Dakkaron/PEPit/SDCardContent/games/farm/gfx/background.bmp

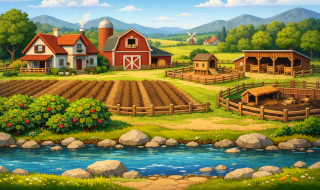
SDCardContent/games/farm/gfx/background.bmp
