Dakkaron/PEPit/SDCardContent/games/farm/gfx/farm1.bmp

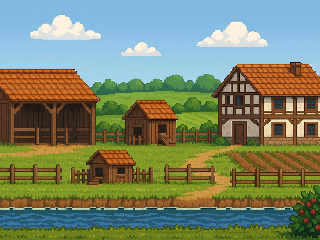
SDCardContent/games/farm/gfx/farm1.bmp
