Dakkaron/PEPit/SDCardContent/games/farm/gfx/farm1_c.bmp

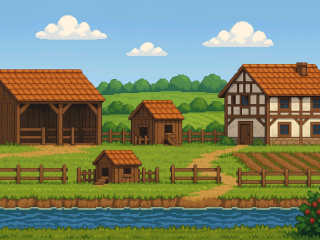
SDCardContent/games/farm/gfx/farm1_c.bmp
