Dakkaron/PEPit/SDCardContent/games/farm/gfx/farm2_c.bmp

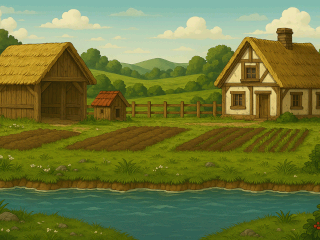
SDCardContent/games/farm/gfx/farm2_c.bmp
