Dakkaron/PEPit/SDCardContent/games/farm/gfx/farm3.bmp

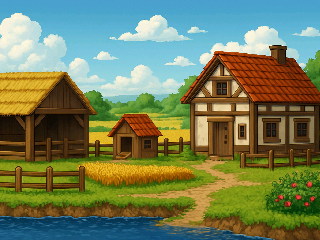
SDCardContent/games/farm/gfx/farm3.bmp
