Dakkaron/PEPit/SDCardContent/games/farm/gfx/farm3_c.bmp

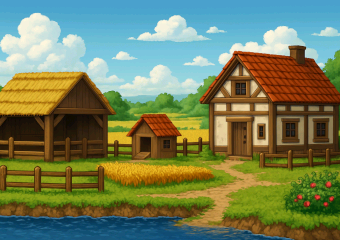
SDCardContent/games/farm/gfx/farm3_c.bmp
