Dakkaron/PEPit/SDCardContent/games/farm/gfx/field_tilled.bmp

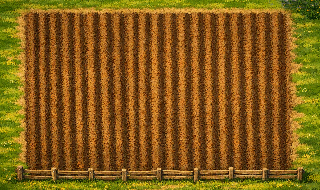
SDCardContent/games/farm/gfx/field_tilled.bmp
