Dakkaron/PEPit/SDCardContent/games/farm/gfx/fish.bmp

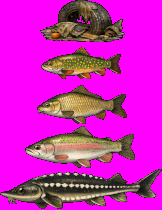
SDCardContent/games/farm/gfx/fish.bmp
