Dakkaron/PEPit/SDCardContent/games/farm/gfx/win/1.bmp

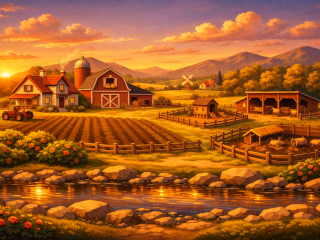
SDCardContent/games/farm/gfx/win/1.bmp
