Dakkaron/PEPit/SDCardContent/games/horserace/gfx/win/1.bmp

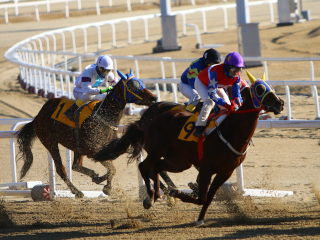
SDCardContent/games/horserace/gfx/win/1.bmp
