Dakkaron/PEPit/SDCardContent/games/plane/gfx/background.bmp

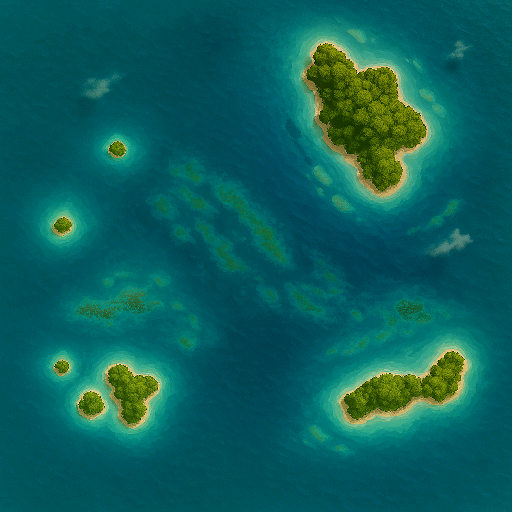
SDCardContent/games/plane/gfx/background.bmp
