Dakkaron/PEPit/SDCardContent/games/plane/gfx/win/win1.bmp

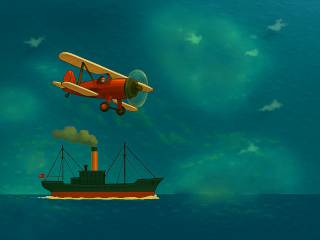
SDCardContent/games/plane/gfx/win/win1.bmp
