Dakkaron/PEPit/SDCardContent/gfx/manometerWinscreen.bmp

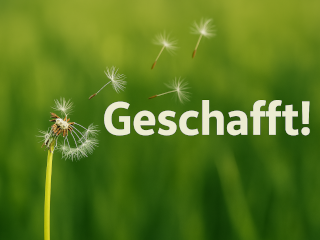
SDCardContent/gfx/manometerWinscreen.bmp
