Dakkaron/PEPit/SDCardContent/gfx/peps_1.5.bmp

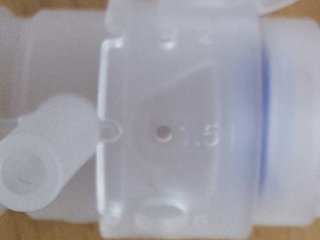
SDCardContent/gfx/peps_1.5.bmp
