Dakkaron/PEPit/SDCardContent/gfx/peps_2.bmp

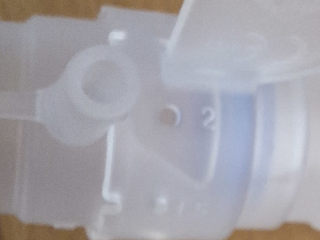
SDCardContent/gfx/peps_2.bmp
