Dakkaron/PEPit/SDCardContent/gfx/peps_3.bmp

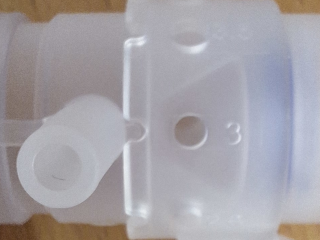
SDCardContent/gfx/peps_3.bmp
