Dakkaron/PEPit/SDCardContent/gfx/peps_4.5.bmp

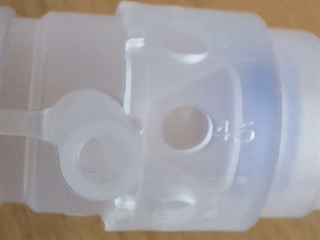
SDCardContent/gfx/peps_4.5.bmp
