Dakkaron/PEPit/SDCardContent/gfx/peps_4.bmp

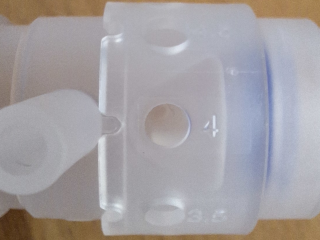
SDCardContent/gfx/peps_4.bmp
