Dakkaron/PEPit/T-HMI-PEPmonitor/src/hardware/pressuresensor.h

#ifndef __PRESSURESENSOR_H__
#define __PRESSURESENSOR_H__

#include <Arduino.h>
#include "constants.h"

void initPressureSensor(String* errorMessage);
void readPressure(BlowData* blowData);
void powerDownPressureSensor(bool down);

#endif /*PRESSURESENSOR*/
