Dakkaron/PEPit/T-HMI-PEPmonitor/src/physioProtocolHandler.cpp

#include "physioProtocolHandler.h"
#include "hardware/sdHandler.h"
#include "hardware/bluetoothHandler.h"
#include "hardware/wifiHandler.h"
#include "hardware/powerHandler.h"
#include "hardware/touchHandler.h"
#include "hardware/pressuresensor.h"
#include "hardware/serialHandler.h"
#include "games/games.h"
#include "constants.h"
#include "updateHandler.h"
#include "systemStateHandler.h"
#include "hardware/joystickHandler.h"

#define INHALE_ICON_PATH "/gfx/inhale.bmp"
#define EXHALE_ICON_PATH "/gfx/exhale.bmp"

static TFT_eSprite inhaleIcon(&tft);
static TFT_eSprite exhaleIcon(&tft);

ProfileData profileData{};
uint32_t currentTask;
uint32_t currentCycle;

BlowData blowData;
JumpData jumpData;

uint32_t lastMs = 0;

void runGameSelection(uint32_t requiredTaskTypes) {
  spr.fillSprite(TFT_BLACK);
  spr.pushSpriteFast(0,0);
  spr.fillSprite(TFT_BLACK);
  tft.fillScreen(TFT_BLACK);
  String errorMessage;
  uint16_t numberOfGames = getNumberOfGames(&errorMessage, requiredTaskTypes);
  checkFailWithMessage(errorMessage);
  Serial.print("Number of games: ");
  Serial.println(numberOfGames);
  String gamePath;
  if (numberOfGames == 0) {
    checkFailWithMessage("No fitting game found!");
  } else {
    gamePath = getGamePath(displayGameSelection(&spr, numberOfGames, requiredTaskTypes, &errorMessage), requiredTaskTypes, &errorMessage);
  }
  checkFailWithMessage(errorMessage);
  Serial.print("Game path: ");
  Serial.println(gamePath);
  displayFullscreenMessage("Spiel wird geladen\nBitte warten...");
  initGames(gamePath, &errorMessage);
  checkFailWithMessage(errorMessage);
}

uint32_t runProfileSelection() {
  String errorMessage;
  bool profileSuccessfullyLoaded = false;
  uint32_t requiredTaskTypes = 0;
  while (!profileSuccessfullyLoaded) {
    spr.fillSprite(TFT_BLACK);
    spr.pushSpriteFast(0,0);
    spr.fillSprite(TFT_BLACK);
    tft.fillScreen(TFT_BLACK);
    uint32_t totalNumberOfProfiles = getNumberOfProfiles(&errorMessage);
    checkFailWithMessage(errorMessage);
    int32_t selectedProfileId = displayProfileSelection(&spr, totalNumberOfProfiles, &errorMessage);
    profileSuccessfullyLoaded = true;
    if (selectedProfileId == PROGRESS_MENU_SELECTION_ID) {
      runGameSelection(REQUIRED_TASK_TYPE_PROGRESSION_MENU);
      uint32_t ms = millis();
      spr.fillSprite(TFT_BLACK);
      while (displayProgressionMenu(&spr, &errorMessage)) {
        checkFailWithMessage(errorMessage);
        lastMs = ms;
        ms = millis();
        doSystemTasks();
        spr.pushSpriteFast(0,0);
        spr.fillSprite(TFT_BLACK);
        handleSerial();
        vTaskDelay(1); // watchdog
      }
      tft.fillScreen(TFT_BLACK);
      deepSleepReset(); // Todo: don't restart, just go back to profile selection, but clear running game data
      
      profileSuccessfullyLoaded = false;
      continue;
    } else if (selectedProfileId == EXECUTION_LIST_SELECTION_ID) {
      spr.fillSprite(TFT_BLACK);
      spr.pushSpriteFast(0,0);
      tft.fillScreen(TFT_BLACK);
      char* executionLog;
      if (SD_MMC.exists(EXECUTION_LOG_PATH)) {
        executionLog = readFileToNewPSBuffer(EXECUTION_LOG_PATH);
      } else {
        executionLog = new char[1];
        executionLog[0] = '\0';
      }
      while (displayExecutionList(&spr, executionLog, &errorMessage)) {
        uint32_t ms = millis();
        checkFailWithMessage(errorMessage);
        lastMs = ms;
        ms = millis();
        doSystemTasks();
        spr.pushSpriteFast(0,0);
        spr.fillSprite(TFT_BLACK);
        handleSerial();
        vTaskDelay(1); // watchdog
      }
      delete(executionLog);
    } else if (selectedProfileId == SYSTEM_UPDATE_SELECTION_ID) {
      spr.fillSprite(TFT_BLACK);
      spr.pushSpriteFast(0,0);
      tft.fillScreen(TFT_BLACK);
      downloadAndRunSystemUpdate(&errorMessage);
      checkFailWithMessage(errorMessage);
      profileSuccessfullyLoaded = false; // Should never happen
      continue;
    }
    checkFailWithMessage(errorMessage);
    readProfileData(selectedProfileId, &profileData, &errorMessage);
    for (uint32_t i=0;i<profileData.tasks;i++) {
      if (profileData.taskType[i] == PROFILE_TASK_TYPE_SHORTBLOWS) {
        requiredTaskTypes |= REQUIRED_TASK_TYPE_SHORTBLOWS;
      } else if (profileData.taskType[i] == PROFILE_TASK_TYPE_LONGBLOWS) {
        requiredTaskTypes |= REQUIRED_TASK_TYPE_LONGBLOWS;
      } else if (profileData.taskType[i] == PROFILE_TASK_TYPE_EQUALBLOWS) {
        requiredTaskTypes |= REQUIRED_TASK_TYPE_EQUALBLOWS;
      } else if (profileData.taskType[i] == PROFILE_TASK_TYPE_INHALATION) {
        requiredTaskTypes |= REQUIRED_TASK_TYPE_INHALATION;
      } else if (profileData.taskType[i] == PROFILE_TASK_TYPE_INHALATIONPEP) {
        requiredTaskTypes |= REQUIRED_TASK_TYPE_INHALATIONPEP;
      } else if (profileData.taskType[i] == PROFILE_TASK_TYPE_TRAMPOLINE) {
        requiredTaskTypes |= REQUIRED_TASK_TYPE_TRAMPOLINE;
        spr.fillSprite(TFT_BLACK);
        spr.pushSpriteFast(0,0);
        spr.fillSprite(TFT_BLACK);
        tft.fillScreen(TFT_BLACK);
        if (!connectToTrampoline(false)) {
          displayFullscreenMessage("Verbinde mit Trampolin...\nTrampolinsensor einschalten!");
        }
        connectToTrampoline(true);
        break;
      }
    }
    vTaskDelay(1); // watchdog
  }
  for (uint32_t i=0;i<profileData.tasks;i++) {
    switch (profileData.taskType[i]) {
    case PROFILE_TASK_TYPE_LONGBLOWS:
      blowData.totalLongBlowRepetitions += profileData.taskRepetitions[i]*profileData.cycles;break;
    case PROFILE_TASK_TYPE_EQUALBLOWS:
      blowData.totalEqualBlowRepetitions += profileData.taskRepetitions[i]*profileData.cycles;break;
    case PROFILE_TASK_TYPE_SHORTBLOWS:
      blowData.totalShortBlowRepetitions += profileData.taskRepetitions[i]*profileData.cycles;break;
    }
  }
  blowData.totalCycleNumber = profileData.cycles;
  blowData.totalTaskNumber = profileData.tasks;
  jumpData.totalCycleNumber = profileData.cycles;
  jumpData.totalTaskNumber = profileData.tasks;
  while (touch.pressed()) {
    vTaskDelay(1);
  }
  return requiredTaskTypes;
}

inline static unsigned long getTaskDurationUntilLastAction() {
  return _max(1, (blowData.blowEndMs!=0 ? blowData.blowEndMs : blowData.taskStartMs) - blowData.taskStartMs);
}

inline static bool isTrampolineTask() {
  return profileData.taskType[currentTask] == PROFILE_TASK_TYPE_TRAMPOLINE;
}

inline static bool isInhalationPEPTask() {
  return profileData.taskType[currentTask] == PROFILE_TASK_TYPE_INHALATIONPEP;
}

inline static bool isInhalationPEPTaskActingLikePEP(BlowData* blowData) {
  return blowData->blowCount & 0x01;
}

inline static bool isInhalationTask() {
  return profileData.taskType[currentTask] == PROFILE_TASK_TYPE_INHALATION;
}

static void drawManometerModeDisplay() {
  spr.fillSprite(TFT_BLACK);
  if (isTrampolineTask()) {
    if (jumpData.msLeft > 0) {

      spr.setCursor(45, 100);
      spr.setTextSize(3);
      spr.print("Übrige Zeit: ");
      int32_t secondsLeft = _max(0, jumpData.msLeft/1000);
      spr.print(secondsLeft / 60);
      spr.print(":");
      if ((secondsLeft % 60) < 10) {
        spr.print("0");
      }
      spr.print(secondsLeft % 60);
    }
  } else {
    spr.drawCircle(SCREEN_WIDTH/2, SCREEN_HEIGHT/2, 100, 0xffff);
    spr.setTextDatum(CC_DATUM);
    spr.setTextSize(2);
    for (int32_t i=-30; i<=30; i+=1) {
      float angleInRadians = i*0.025*PI - PI*0.5;
      float cosI = cos(angleInRadians);
      float sinI = sin(angleInRadians);
      if (i % 10 == 0) {
        spr.drawString(String(i), SCREEN_WIDTH/2 + cosI*60, SCREEN_HEIGHT/2 + sinI*60);
        spr.drawLine(SCREEN_WIDTH/2 + cosI*100, SCREEN_HEIGHT/2 + sinI*100, SCREEN_WIDTH/2 + cosI*80, SCREEN_HEIGHT/2 + sinI*80, 0xffff);
      } else if (i % 5 == 0) {
        spr.drawLine(SCREEN_WIDTH/2 + cosI*100, SCREEN_HEIGHT/2 + sinI*100, SCREEN_WIDTH/2 + cosI*80, SCREEN_HEIGHT/2 + sinI*80, 0xffff);
      } else {
        spr.drawLine(SCREEN_WIDTH/2 + cosI*100, SCREEN_HEIGHT/2 + sinI*100, SCREEN_WIDTH/2 + cosI*90, SCREEN_HEIGHT/2 + sinI*90, 0xffff);
      }
    }
    spr.setTextSize(1);
    spr.setTextDatum(TL_DATUM);
    float angleInRadians = (float)(blowData.pressure)*0.025*PI - PI*0.5;
    float cosI = cos(angleInRadians);
    float sinI = sin(angleInRadians);
    if (cosI>-0.01 && cosI<0.01) {
      cosI = 0.0;
    }
    spr.drawLine(SCREEN_WIDTH*0.5, SCREEN_HEIGHT*0.5, SCREEN_WIDTH*0.5 + cosI*60.0, SCREEN_HEIGHT*0.5 + sinI*60.0, 0xffff);

    spr.fillRect(240, 210, 80, 30, TFT_BLUE);
    spr.setTextSize(2);
    if (blowData.cycleNumber >= blowData.totalCycleNumber-1 && blowData.taskNumber >= blowData.totalTaskNumber-1) {
      spr.drawString("Fertig", 255, 220);
    } else {
      spr.drawString("Weiter", 255, 220);
    }
  }
  doSystemTasks();
  spr.pushSpriteFast(0, 0);
}

static void drawInhalationDisplay() {
  spr.fillSprite(TFT_BLACK);
  String errorMessage;
  drawInhalationGame(&spr, &blowData, &errorMessage);
  drawProgressBar(&spr, blowData.currentlyBlowing ? (100 * (blowData.ms - blowData.blowStartMs) / blowData.targetDurationMs) : 0, 0, PRESSURE_BAR_X, PRESSURE_BAR_Y+25, PRESSURE_BAR_WIDTH, PRESSURE_BAR_HEIGHT);
  checkFailWithMessage(errorMessage);
  
  drawProgressBar(&spr, blowData.pressure, 10, PRESSURE_BAR_X, PRESSURE_BAR_Y, PRESSURE_BAR_WIDTH, PRESSURE_BAR_HEIGHT);
  spr.setTextSize(2);
  spr.setCursor(PRESSURE_BAR_X + 40, PRESSURE_BAR_Y - 14);
  printShaded(&spr, String(blowData.blowCount));
  
  spr.setCursor(PRESSURE_BAR_X + 80, PRESSURE_BAR_Y - 14);
  if (blowData.totalTaskNumber>1 && blowData.totalCycleNumber>1) {
    printShaded(&spr, String(blowData.taskNumber) + "/" + String(blowData.cycleNumber));
  } else if (blowData.totalTaskNumber>1) {
    printShaded(&spr, String(blowData.taskNumber));
  } else if (blowData.totalCycleNumber>1) {
    printShaded(&spr, String(blowData.cycleNumber));
  }
  
  if (blowData.blowCount >= blowData.totalBlowCount) {
    spr.fillRect(240, 210, 80, 30, TFT_BLUE);
    spr.drawString("Fertig", 255, 220);
  }

  doSystemTasks();
  spr.pushSpriteFast(0, 0);
}

static void drawInhaleExhaleIcons(BlowData* blowData) {
  if (!inhaleIcon.created()) {
    loadBmp(&inhaleIcon, INHALE_ICON_PATH);
    loadBmp(&exhaleIcon, EXHALE_ICON_PATH);
  }
  if (blowData->negativePressure) {
    inhaleIcon.pushToSprite(&spr, PRESSURE_BAR_X + PRESSURE_BAR_WIDTH - 32, PRESSURE_BAR_Y - 32, 0xf81f);
  } else {
    exhaleIcon.pushToSprite(&spr, PRESSURE_BAR_X + PRESSURE_BAR_WIDTH - 32, PRESSURE_BAR_Y - 32, 0xf81f);
  }
}

static void drawPEPDisplay() {
  spr.fillSprite(TFT_BLACK);
  String errorMessage;
  switch (blowData.taskType) {
    case PROFILE_TASK_TYPE_LONGBLOWS:
      drawLongBlowGame(&spr, &blowData, &errorMessage);break;
    case PROFILE_TASK_TYPE_EQUALBLOWS:
      drawEqualBlowGame(&spr, &blowData, &errorMessage);break;
    case PROFILE_TASK_TYPE_SHORTBLOWS:
      drawShortBlowGame(&spr, &blowData, &errorMessage);break;
    case PROFILE_TASK_TYPE_INHALATIONPEP:
      drawInhalationBlowGame(&spr, &blowData, &errorMessage);break;
  }
  drawProgressBar(&spr, blowData.currentlyBlowing ? (100 * (blowData.ms - blowData.blowStartMs) / blowData.targetDurationMs) : 0, 0, PRESSURE_BAR_X, PRESSURE_BAR_Y+25, PRESSURE_BAR_WIDTH, PRESSURE_BAR_HEIGHT);
  checkFailWithMessage(errorMessage);
  
  drawProgressBar(&spr, blowData.pressure, 10, PRESSURE_BAR_X, PRESSURE_BAR_Y, PRESSURE_BAR_WIDTH, PRESSURE_BAR_HEIGHT);
  spr.setTextSize(2);
  spr.setCursor(PRESSURE_BAR_X + 40, PRESSURE_BAR_Y - 14);
  printShaded(&spr, String(blowData.blowCount));
  
  spr.setCursor(PRESSURE_BAR_X + 80, PRESSURE_BAR_Y - 14);
  if (blowData.totalTaskNumber>1 && blowData.totalCycleNumber>1) {
    printShaded(&spr, String(blowData.taskNumber) + "/" + String(blowData.cycleNumber));
  } else if (blowData.totalTaskNumber>1) {
    printShaded(&spr, String(blowData.taskNumber));
  } else if (blowData.totalCycleNumber>1) {
    printShaded(&spr, String(blowData.cycleNumber));
  }
  
  if (blowData.taskType == PROFILE_TASK_TYPE_INHALATIONPEP) {
    drawInhaleExhaleIcons(&blowData);
    if (blowData.blowCount >= blowData.totalBlowCount) {
      spr.fillRect(240, 210, 80, 30, TFT_BLUE);
      spr.drawString("Fertig", 255, 220);
    }
  }

  doSystemTasks();
  spr.pushSpriteFast(0, 0);
}

static void drawTrampolineDisplay() {
  spr.fillSprite(TFT_BLACK);
  String errorMessage;
  drawTrampolineGame(&spr, &jumpData, &errorMessage);
  checkFailWithMessage(errorMessage);
  if (jumpData.msLeft > 0) {
    drawProgressBar(&spr, (100L*(jumpData.totalTime-jumpData.msLeft))/jumpData.totalTime, 0, PRESSURE_BAR_X, PRESSURE_BAR_Y, PRESSURE_BAR_WIDTH, PRESSURE_BAR_HEIGHT);
    spr.setTextSize(2);
    spr.drawString(String(jumpData.jumpCount) + "/" + String(jumpData.highscore), PRESSURE_BAR_X + 20, PRESSURE_BAR_Y - 14);
    spr.setCursor(100, 5);
    spr.setTextSize(3);
    int32_t secondsLeft = _max(0, jumpData.msLeft/1000);
    spr.print(secondsLeft / 60);
    spr.print(":");
    if ((secondsLeft % 60) < 10) {
      spr.print("0");
    }
    spr.print(secondsLeft % 60);
  }
  doSystemTasks();
  spr.pushSpriteFast(0, 0);
}

static void handleLogExecutions() {
  uint32_t textDatumBak = tft.getTextDatum();

  spr.fillSprite(TFT_BLACK);
  spr.setTextSize(2);
  spr.setTextDatum(TL_DATUM);
  spr.drawString("Datum und Uhrzeit", 20, 100);
  spr.drawString("werden abgerufen.", 20, 120);
  spr.drawString("Bitte warten...", 20, 140);
  spr.pushSpriteFast(0,0);

  String errorMessage;
  String ntpDateString, ntpTimeString;
  getFormattedTime(&ntpDateString, &ntpTimeString, &errorMessage);
  checkSoftFailWithMessage(errorMessage);
  if (!errorMessage.isEmpty()) {
    displayDateTimeSelection();
    errorMessage = "";
    getFormattedTime(&ntpDateString, &ntpTimeString, &errorMessage);
    checkSoftFailWithMessage(errorMessage);
    if (!errorMessage.isEmpty()) { // Should never happen
      ntpDateString = "N/A";
      ntpTimeString = "N/A";
      errorMessage = "";
    }
  }
  Serial.println("NTP Time: " + ntpDateString + " " + ntpTimeString);

  spr.fillSprite(TFT_BLACK);
  spr.setTextDatum(TC_DATUM);
  spr.setTextSize(2);
  spr.drawString("Schreibe Log auf SD-Karte", 160, 120);
  spr.drawString("NICHT AUSSCHALTEN!", 160, 140);
  spr.setTextDatum(textDatumBak);
  spr.pushSpriteFast(0,0);

  logExecutionToSD(&profileData, ntpDateString, ntpTimeString, blowData.successes, blowData.fails, blowData.totalTimeSpentBreathing, &errorMessage);
  checkFailWithMessage(errorMessage);
}

static void drawFinished() {
  static uint32_t winscreenTimeout = 0;
  static String winScreenPath = "";
  if (winscreenTimeout == 0) { // Only runs on first execution
    Serial.print("##### Start drawFinished(): ");
    Serial.println(millis());
    String errorMessage;
    Serial.print("##### Start handleLogExecutions(): ");
    Serial.println(millis());
    if (systemConfig.logExecutions) {
      handleLogExecutions();
    }
    Serial.print("##### initializing win screen: ");
    Serial.println(millis());
    endGame(&errorMessage);
    checkFailWithMessage(errorMessage);
    winscreenTimeout = millis() + WIN_SCREEN_TIMEOUT;
    spr.frameBuffer(1); // Clearing both frame buffers to get rid of old content
    spr.fillSprite(TFT_GREEN);
    spr.frameBuffer(2);
    spr.fillSprite(TFT_GREEN);
    spr.frameBuffer(1);
    spr.fillSprite(TFT_BLACK);
    spr.frameBuffer(2);
    spr.fillSprite(TFT_BLACK);
    spr.pushSpriteFast(0,0);
    tft.fillScreen(TFT_BLACK);
    Serial.print("##### start displaying win screen: ");
    Serial.println(millis());
    while (displayWinScreen(&spr, &errorMessage) && millis() < winscreenTimeout) {
      checkFailWithMessage(errorMessage);
      spr.pushSpriteFast(0,0);
      spr.fillSprite(TFT_BLACK);
      handleSerial();
      doSystemTasks();
      vTaskDelay(1); // watchdog
      if (isTouchInZone(0, 0, SCREEN_WIDTH, SCREEN_HEIGHT)) {
        winscreenTimeout = millis() + WIN_SCREEN_TIMEOUT;
      }
    }
    Serial.print("##### Display winscreen done: ");
    Serial.println(millis());
    if (systemConfig.manometerMode) {
      winScreenPath = MANOMETER_WINSCREEN_PATH;
    } else {
      winScreenPath = getRandomWinScreenPathForCurrentGame(&errorMessage);
      Serial.println("Win screen path: "+winScreenPath);
      checkFailWithMessage(errorMessage);
    }
    spr.frameBuffer(1);
    spr.fillSprite(TFT_BLACK);
    spr.frameBuffer(2);
    spr.fillSprite(TFT_BLACK);
    tft.fillScreen(TFT_BLACK);
    drawBmp(winScreenPath, 0, 0);
    if (getSystemUpdateAvailableStatus() == FIRMWARE_UPDATE_AVAILABLE) {
      uint32_t beforeShowUpdateTimeout = millis() + SHOW_SYSTEM_UPDATE_ON_WINSCREEN_TIMEOUT;
      Serial.print("Starting update timeout: ");
      Serial.print(beforeShowUpdateTimeout);
      Serial.print(" . ");
      Serial.println(millis());
      while (millis() < beforeShowUpdateTimeout) {
        spr.fillRect(32,0,66,20,TFT_BLACK);
        doSystemTasks();
        spr.pushSpriteFast(0,0);
        vTaskDelay(1); // watchdog
      }
      Serial.println("Ending update timeout.");

      tft.fillRect(25, 25, 270, 190, 0x001F);
      tft.fillRect(30, 30, 260, 180, 0x94b2);
      drawBmp("/gfx/systemupdate.bmp", 144, 35, false);
      // TODO: Add joystick controls for the update/reboot buttons
      tft.setTextColor(0xFFFF);
      tft.setTextSize(2);
      tft.setTextDatum(1);
      tft.drawString("Update verfügbar", 160, 80);
      tft.fillRect(60, 110, 200, 45, COLOR_BUTTON_PRIMARY);
      tft.drawString("Update jetzt starten", 160, 125);
      tft.fillRect(60, 160, 200, 45, COLOR_BUTTON_PRIMARY);
      tft.drawString("Neustart", 160, 175);
      bool isUpdateStarted = false;
      winscreenTimeout = millis() + WIN_SCREEN_TIMEOUT;
      Serial.print("Starting winscreen timeout: ");
      Serial.print(winscreenTimeout);
      Serial.print(" . ");
      Serial.println(millis());
      while (millis() < winscreenTimeout && !isUpdateStarted) {
        isUpdateStarted = isTouchInZone(60, 110, 200, 45);
        if (isTouchInZone(60, 160, 200, 45)) {
          tft.fillScreen(TFT_BLACK);
          deepSleepReset();
        }
        Serial.print(winscreenTimeout);
        Serial.print(" . ");
        Serial.print(millis());
        Serial.print(" - ");
        Serial.println(isUpdateStarted);
        spr.fillRect(32,0,66,20,TFT_BLACK);
        doSystemTasks();
        spr.pushSpriteFast(0,0);
        vTaskDelay(1); // watchdog
      }
      Serial.print("Ending winscreen timeout: ");
      Serial.println(isUpdateStarted);
      if (isUpdateStarted) {
        Serial.println("Starting update.");
        String errorMessage;
        tft.fillScreen(TFT_BLACK);
        downloadAndRunSystemUpdate(&errorMessage);
        checkFailWithMessage(errorMessage);
      } else {
        Serial.println("Power off.");
        power_off();
      }
    } else {
      tft.setTextDatum(1);
      tft.setTextColor(COLOR_BUTTON_PRIMARY_TEXT);
      if (isJoystickPresent()) {
        tft.fillRect(55, 175, 210, 55, TFT_YELLOW);
        tft.fillRect(58, 178, 204, 49, COLOR_BUTTON_PRIMARY);
      } else {
        tft.fillRect(55, 175, 210, 55, COLOR_BUTTON_PRIMARY_FRAME);
        tft.fillRect(60, 180, 200, 45, COLOR_BUTTON_PRIMARY);
      }
      tft.drawString("Neustart", 160, 195);
    }
  } else if (millis() > winscreenTimeout) {
    power_off();
  }
  if (getSystemUpdateAvailableStatus() != FIRMWARE_UPDATE_AVAILABLE && (isTouchInZone(60, 160, 200, 45) || getJoystickButton())) {
    tft.fillScreen(TFT_BLACK);
    deepSleepReset();
  }
  spr.fillRect(32,0,66,20,TFT_BLACK);
  doSystemTasks();
  spr.pushSpriteFast(0,0);
}

void displayPhysioRotateScreen() {
  if (profileData.taskChangeImagePath[currentTask].isEmpty() && profileData.taskChangeMessage[currentTask].isEmpty()) {
    return;
  }
  spr.fillSprite(TFT_BLACK);
  spr.pushSpriteFast(0, 0);
  spr.fillSprite(TFT_BLACK);
  spr.setTextSize(4);
  drawBmp(profileData.taskChangeImagePath[currentTask], 0, 0);
  spr.setTextDatum(TL_DATUM);
  spr.drawString(profileData.taskChangeMessage[currentTask], 5, 5);
  spr.pushSpriteFast(0, 0);
  uint32_t displayOkButtonMs = millis() + 5000;
  boolean joystickLocked = getJoystickButton();

  while (!isTouchInZone(230, 170, 80, 60) && (joystickLocked || !getJoystickButton())) {
    if (joystickLocked && !getJoystickButton()) {
      joystickLocked = false;
    }
    if (displayOkButtonMs!=0 && millis() > displayOkButtonMs) {
      spr.fillSprite(TFT_BLACK);
      spr.pushSpriteFast(0, 0);
      spr.fillSprite(TFT_BLACK);
      spr.setTextSize(4);
      drawBmp(profileData.taskChangeImagePath[currentTask], 0, 0);
      spr.setTextDatum(TL_DATUM);
      spr.drawString(profileData.taskChangeMessage[currentTask], 5, 5);
      if (isJoystickPresent()) {
        spr.fillRect(230, 170, 80, 60, TFT_YELLOW);
        spr.fillRect(233, 173, 74, 54, 0x18db);
      } else {
        spr.fillRect(230, 170, 80, 60, 0x18db);
      }
      spr.drawString("OK", 245, 185);
      spr.pushSpriteFast(0, 0);
      displayOkButtonMs = 0;
    }
    handleSerial();
    doSystemTasks();
    vTaskDelay(1); // watchdog
  }
  
  tft.fillScreen(TFT_BLACK);
  spr.fillScreen(TFT_BLACK);
  spr.pushSpriteFast(0, 0);
  delay(200);
}

inline static unsigned long getLastBlowEvent() {
  return blowData.currentlyBlowing ? blowData.blowStartMs : blowData.blowEndMs;
}

inline static bool isPepTask() {
  switch (profileData.taskType[currentTask]) {
    case PROFILE_TASK_TYPE_LONGBLOWS:
    case PROFILE_TASK_TYPE_EQUALBLOWS:
    case PROFILE_TASK_TYPE_SHORTBLOWS:
      return true;
    default:
      return false;
    }
}

void handlePhysioTask() {
  static uint32_t taskFinishedTimeout = 0;
  static bool touchBlocked = false;
  lastMs = blowData.ms;
  blowData.ms = millis();
  jumpData.ms = blowData.ms;
  if (blowData.taskStartMs == 0) {
    blowData.taskStartMs = blowData.ms;
  }
  if (isTrampolineTask()) {
    if (jumpData.msLeft < -5000) {
      currentCycle++;
      drawFinished(); //Todo: Make jump task compatible with multi-task configs
      return;
    }

    jumpData.cycleNumber = currentCycle;
    jumpData.taskNumber = currentTask;
    jumpData.totalTime = profileData.taskTime[currentTask];

    getJumpData(&jumpData, &profileData, currentTask);
  } else {
    blowData.taskNumber = currentTask;
    blowData.cycleNumber = currentCycle;
    blowData.totalBlowCount = profileData.taskRepetitions[currentTask];
    blowData.taskType = profileData.taskType[currentTask];
    if (isPepTask() || isInhalationTask() || (isInhalationPEPTask() && !isInhalationPEPTaskActingLikePEP(&blowData))) {
      blowData.targetPressure = profileData.taskTargetStrength[currentTask];
      blowData.minPressure = 100*profileData.taskMinStrength[currentTask]/profileData.taskTargetStrength[currentTask];
      blowData.negativePressure = profileData.taskNegativeStrength[currentTask];
      blowData.targetDurationMs = profileData.taskTime[currentTask];
    } else { // InhalationPEP task acting in PEP mode
      blowData.targetPressure = profileData.taskTargetStrength2[currentTask];
      blowData.minPressure = 100*profileData.taskMinStrength2[currentTask]/profileData.taskTargetStrength2[currentTask];
      blowData.negativePressure = profileData.taskNegativeStrength2[currentTask];
      blowData.targetDurationMs = profileData.taskTime2[currentTask];
    }

    if (currentCycle >= blowData.totalCycleNumber) {
      drawFinished();
      return;
    }
    readPressure(&blowData);
    if (blowData.pressure>blowData.minPressure && !blowData.currentlyBlowing) {
      Serial.print(F("Blowing... "));
      blowData.currentlyBlowing = true;
      blowData.blowStartMs = blowData.ms;
      blowData.peakPressure = 0;
      blowData.cumulativeError = 0;
      blowData.lastBlowStatus |= NEW_BLOW;
    } else if (blowData.pressure<=blowData.minPressure && blowData.currentlyBlowing) {
      blowData.blowEndMs = blowData.ms;
      blowData.totalTimeSpentBreathing += blowData.blowEndMs-blowData.blowStartMs;
      blowData.breathingScore = 200 * blowData.totalTimeSpentBreathing / getTaskDurationUntilLastAction();
      Serial.print(blowData.blowEndMs-blowData.blowStartMs);
      Serial.println(F("ms"));
      blowData.currentlyBlowing = false;
      Serial.print(F("Ending blow"));
      if (blowData.ms-blowData.blowStartMs > blowData.targetDurationMs) {
        blowData.blowCount++;
        blowData.lastBlowStatus = LAST_BLOW_SUCCEEDED;
        blowData.successes++;
        Serial.println(F(" successfully"));
        Serial.print(F(" Blowstart:       "));
        Serial.println(blowData.blowStartMs);
        Serial.print(F(" Blowend:         "));  
        Serial.println(blowData.blowEndMs);
        Serial.print(F(" Target Duration: "));
        Serial.println(blowData.targetDurationMs);
        // Check for task end on PEP tasks
        if (!systemConfig.manometerMode && isPepTask() && taskFinishedTimeout==0 && blowData.blowCount >= blowData.totalBlowCount) {
          taskFinishedTimeout = blowData.ms + 2000;
        }
      } else {
        blowData.fails++;
        blowData.lastBlowStatus = LAST_BLOW_FAILED;
      }
    }
    // Check for task end on inhalation tasks
    if (blowData.blowCount >= blowData.totalBlowCount) {
      if (isTouchInZone(240, 210, 80, 30)) {
        taskFinishedTimeout = blowData.ms;
        tft.invertDisplay(0);
      } else if ((isInhalationTask() || isInhalationPEPTask()) && !blowData.currentlyBlowing && blowData.ms-getLastBlowEvent() > INHALATION_TASK_END_TIMEOUT && taskFinishedTimeout==0) {
        taskFinishedTimeout = blowData.ms;
        tft.invertDisplay(0);
      } else if ((isInhalationTask() || isInhalationPEPTask()) && !blowData.currentlyBlowing && blowData.ms-getLastBlowEvent() > INHALATION_TASK_WARN_TIMEOUT) {
        tft.invertDisplay((blowData.ms/500) % 2);
      } else {
        tft.invertDisplay(0);
      }
    }
    if (systemConfig.manometerMode && !touchBlocked && isTouchInZone(240, 210, 80, 30)) {
      if (isTouchInZone(240, 210, 80, 30)) {
        taskFinishedTimeout = blowData.ms;
        tft.invertDisplay(0);
      }
    }
    blowData.peakPressure = _max(blowData.peakPressure, blowData.pressure);
    if (taskFinishedTimeout!=0 && blowData.ms > taskFinishedTimeout) {
      Serial.println();
      Serial.println("##### DISPLAY ROTATE ######");
      Serial.print("    Rotating to: ");
      switch (blowData.taskType) {
        case PROFILE_TASK_TYPE_EQUALBLOWS:
          Serial.print("Equal blows");break;
        case PROFILE_TASK_TYPE_LONGBLOWS:
          Serial.print("Long blows");break;
        case PROFILE_TASK_TYPE_SHORTBLOWS:
          Serial.print("Short blows");break;
        case PROFILE_TASK_TYPE_TRAMPOLINE:
          Serial.print("Trampoline");break;
        case PROFILE_TASK_TYPE_INHALATION:
          Serial.print("Inhalation");break;
        case PROFILE_TASK_TYPE_INHALATIONPEP:
          Serial.print("Inhalation+PEP");break;
      }
      Serial.println();
      currentTask++;
      if (currentTask >= profileData.tasks) {
        currentCycle++;
        currentTask = 0;
      }
      blowData.blowCount = 0;
      blowData.lastBlowStatus = 0;
      blowData.taskStartMs = blowData.ms;
      taskFinishedTimeout = 0;
      if (currentCycle < blowData.totalCycleNumber) {
        displayPhysioRotateScreen();
      }
    }
  }

  if (systemConfig.manometerMode) {
    drawManometerModeDisplay();
  } else if (isPepTask() || isInhalationPEPTask()) {
    drawPEPDisplay();
  } else if (isInhalationTask()) {
    drawInhalationDisplay();
  } else if (isTrampolineTask()) {
    drawTrampolineDisplay();
  }
  if (!isTouchInZone(0, 0, SCREEN_WIDTH, SCREEN_HEIGHT)) {
    touchBlocked = false;
  }
}
