Dakkaron/PEPit/T-HMI-PEPmonitor/src/hardware/MyFont.h

/**
 * Created with gfx-fe (github.com/arnoson/gfx-fe): a web based editor for gfx fonts.
 * Editor Settings: {"canvas":{"width":8,"height":8},"metrics":{},"baseline":2,"basedOn":{"name":"","size":12,"guides":true,"threshold":125}}
 */

const uint8_t Font5x7FixedBitmaps[] PROGMEM = {
  0xfa, 0xb4, 0x52, 0xbe, 0xaf, 0xa9, 0x40, 0x23, 0xe8, 0xe2, 0xf8, 0x80,
  0xc6, 0x44, 0x44, 0x4c, 0x60, 0x64, 0xa8, 0x8a, 0xc9, 0xa0, 0xd8, 0x6a,
  0xa4, 0x95, 0x58, 0x25, 0x5d, 0xf7, 0x54, 0x80, 0x21, 0x3e, 0x42, 0x00,
  0xd0, 0xf8, 0xf0, 0x08, 0x88, 0x88, 0x00, 0x74, 0x67, 0x5c, 0xc5, 0xc0,
  0x59, 0x24, 0xb8, 0x74, 0x42, 0x22, 0x23, 0xe0, 0xf8, 0x88, 0x20, 0xc5,
  0xc0, 0x11, 0x95, 0x2f, 0x88, 0x40, 0xfc, 0x21, 0xe0, 0xc5, 0xc0, 0x32,
  0x21, 0xe8, 0xc5, 0xc0, 0xf8, 0x44, 0x44, 0x21, 0x00, 0x74, 0x62, 0xe8,
  0xc5, 0xc0, 0x74, 0x62, 0xf0, 0x89, 0x80, 0xf3, 0xc0, 0xf3, 0x60, 0x12,
  0x48, 0x42, 0x10, 0xf8, 0x3e, 0x84, 0x21, 0x24, 0x80, 0x74, 0x42, 0x22,
  0x00, 0x80, 0x74, 0x6b, 0x7b, 0xc1, 0xc0, 0x22, 0xa3, 0xf8, 0xc6, 0x20,
  0xf4, 0x63, 0xe8, 0xc7, 0xc0, 0x74, 0x61, 0x08, 0x45, 0xc0, 0xe4, 0xa3,
  0x18, 0xcb, 0x80, 0xfc, 0x21, 0xe8, 0x43, 0xe0, 0xfc, 0x21, 0xe8, 0x42,
  0x00, 0x74, 0x61, 0x38, 0xc5, 0xc0, 0x8c, 0x63, 0xf8, 0xc6, 0x20, 0xe9,
  0x24, 0xb8, 0x38, 0x84, 0x21, 0x49, 0x80, 0x8c, 0xa9, 0x8a, 0x4a, 0x20,
  0x84, 0x21, 0x08, 0x43, 0xe0, 0x8e, 0xeb, 0x18, 0xc6, 0x20, 0x8c, 0x73,
  0x59, 0xc6, 0x20, 0x74, 0x63, 0x18, 0xc5, 0xc0, 0xf4, 0x63, 0xe8, 0x42,
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
  {    0,    0,    0,    0,    0,    0 }, // 0xb7 '·'
  {    0,    0,    0,    0,    0,    0 }, // 0xb8 '¸'
  {    0,    0,    0,    0,    0,    0 }, // 0xb9 '¹'
  {    0,    0,    0,    0,    0,    0 }, // 0xba 'º'
  {    0,    0,    0,    0,    0,    0 }, // 0xbb '»'
  {    0,    0,    0,    0,    0,    0 }, // 0xbc '¼'
  {    0,    0,    0,    0,    0,    0 }, // 0xbd '½'
  {    0,    0,    0,    0,    0,    0 }, // 0xbe '¾'
  {    0,    0,    0,    0,    0,    0 }, // 0xbf '¿'
  {    0,    0,    0,    0,    0,    0 }, // 0xc0 'À'
  {    0,    0,    0,    0,    0,    0 }, // 0xc1 'Á'
  {    0,    0,    0,    0,    0,    0 }, // 0xc2 'Â'
  {    0,    0,    0,    0,    0,    0 }, // 0xc3 'Ã'
  {  356,    5,    7,    6,    0,    0 }, // 0xc4 'Ä'
  {    0,    0,    0,    0,    0,    0 }, // 0xc5 'Å'
  {    0,    0,    0,    0,    0,    0 }, // 0xc6 'Æ'
  {    0,    0,    0,    0,    0,    0 }, // 0xc7 'Ç'
  {    0,    0,    0,    0,    0,    0 }, // 0xc8 'È'
  {    0,    0,    0,    0,    0,    0 }, // 0xc9 'É'
  {    0,    0,    0,    0,    0,    0 }, // 0xca 'Ê'
  {    0,    0,    0,    0,    0,    0 }, // 0xcb 'Ë'
  {    0,    0,    0,    0,    0,    0 }, // 0xcc 'Ì'
  {    0,    0,    0,    0,    0,    0 }, // 0xcd 'Í'
  {    0,    0,    0,    0,    0,    0 }, // 0xce 'Î'
  {    0,    0,    0,    0,    0,    0 }, // 0xcf 'Ï'
  {    0,    0,    0,    0,    0,    0 }, // 0xd0 'Ð'
  {    0,    0,    0,    0,    0,    0 }, // 0xd1 'Ñ'
  {    0,    0,    0,    0,    0,    0 }, // 0xd2 'Ò'
  {    0,    0,    0,    0,    0,    0 }, // 0xd3 'Ó'
  {    0,    0,    0,    0,    0,    0 }, // 0xd4 'Ô'
  {    0,    0,    0,    0,    0,    0 }, // 0xd5 'Õ'
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
};

const GFXfont Font5x7Fixed PROGMEM = {
  (uint8_t *)Font5x7FixedBitmaps,
  (GFXglyph *)Font5x7FixedGlyphs,
  32, 252, 8
};
