Dakkaron/PEPit/T-HMI-PEPmonitor/src/hardware/wifiHandler.cpp

#include "wifiHandler.h"
#include <WiFi.h>
#include <ArduinoJson.h>
#include <HTTPClient.h>
#include "sdHandler.h"
#include "esp32-hal.h"

static uint8_t wifiStatus = WIFI_CONNECTION_SEARCHING;

uint8_t getWifiStatus() {
  return wifiStatus;
}

uint8_t startWifi() {
  String ssid = "";
  String password = "";
  if (wifiStatus == WIFI_CONNECTION_OK) {
    return wifiStatus;
  }
  int32_t networksFound = WiFi.scanNetworks();
  for (int32_t wifiNumber=0; wifiNumber<MAX_WIFI_NETWORKS; wifiNumber++) {
    Serial.println("Starting WIFI");
    WiFi.mode(WIFI_STA);
    switch (wifiNumber) {
      case 0:
        ssid = systemConfig.wifiSsid;
        password = systemConfig.wifiPassword;
        break;
      case 1:
        ssid = systemConfig.wifiSsid2;
        password = systemConfig.wifiPassword2;
        break;
      case 2:
        ssid = systemConfig.wifiSsid3;
        password = systemConfig.wifiPassword3;
        break;
    }
    Serial.print(wifiNumber+1);
    Serial.print("/");
    Serial.println(MAX_WIFI_NETWORKS);
    Serial.println(ssid);
    Serial.println(password);
    bool wifiFound = false;
    for (int32_t i=0;i<networksFound;i++) {
      if (WiFi.SSID(i) == ssid) {
        wifiFound = true;
        break;
      }
    }
    if (!wifiFound) {
      Serial.println("Wifi not found");
      wifiStatus = WIFI_CONNECTION_NOWIFI;
      continue;
    }
    WiFi.begin(ssid, password);
    Serial.print("Connecting to WIFI");
    for (uint8_t i=0;i<WIFI_RETRY_COUNT;i++) {
      if (WiFi.status() != WL_CONNECTED) {
        Serial.print('.');
        delay(1000);
      } else {
        wifiStatus = WIFI_CONNECTION_OK;
        Serial.println("done");
        return wifiStatus;
      }
    }
    Serial.println("Failed to connect to WIFI "+ssid);
  }
  Serial.println("ENDING WIFI CONNECT");
  return wifiStatus;
}

static String leftPad(String s, uint16_t len, String c) {
  uint32_t charsToAdd = len-s.length();
  for (uint32_t i=0; i<charsToAdd; i++) {
    s = c + s;
  }
  return s;
}

void getFormattedTime(String* ntpDateString, String* ntpTimeString, String* errorMessage) {
  static int32_t lastWifiStatus = -1;
  static bool getLocalTimeFailedBefore = false;
  struct tm timeinfo;
  if((wifiStatus==lastWifiStatus && getLocalTimeFailedBefore) || !getLocalTime(&timeinfo,1)){
    if (!(wifiStatus==lastWifiStatus && getLocalTimeFailedBefore)) {
      Serial.println("Failed to obtain time from NTP");
    }
    getLocalTimeFailedBefore = true;
    lastWifiStatus = wifiStatus;
    errorMessage->concat("Konnte Zeit nicht abrufen.\n");
    errorMessage->concat("Wahrscheinlich WLAN-Verbindungsproblem.\n");
    *ntpDateString = "N/A";
    *ntpTimeString = "N/A";
    return;
  }
  *ntpDateString = String(timeinfo.tm_year+1900) + "-" + String(timeinfo.tm_mon+1) + "-" + String(timeinfo.tm_mday);
  *ntpTimeString = leftPad(String(timeinfo.tm_hour), 2, "0") + ":" + leftPad(String(timeinfo.tm_min), 2, "0");
}

void downloadFile(String url, String filename, String* errorMessage, THandlerFunction_Progress progressCallback) {
  // Get file stream from internet
  uint32_t connectionStatus = startWifi();
  if (connectionStatus == WIFI_CONNECTION_NOWIFI) {
    errorMessage->concat("Failed to download file from ");
    errorMessage->concat(url);
    errorMessage->concat(" because of missing WIFI connection");
    return;
  }

  HTTPClient httpClient;
  httpClient.setFollowRedirects(HTTPC_STRICT_FOLLOW_REDIRECTS);
  Serial.println("downloadFile("+url+", "+filename+")");
  httpClient.begin(url);
  int httpCode = httpClient.GET();
  if (httpCode != 200) {
    errorMessage->concat("HTTP error: "+String(httpCode));
    return;
  }
  WiFiClient* stream = httpClient.getStreamPtr();

  // Download data and write into SD card
  size_t downloadedDataSize = 0;
  const size_t FILE_SIZE = httpClient.getSize();
  uint8_t* fileBuffer = (uint8_t*)heap_caps_malloc(FILE_DOWNLOAD_CHUNK_SIZE+1, MALLOC_CAP_SPIRAM);
  File file = SD_MMC.open(filename, FILE_WRITE, true);
  Serial.println("Starting download");
  while (downloadedDataSize < FILE_SIZE) {
    size_t availableDataSize = stream->available();
    if (availableDataSize > 0) {
      uint32_t bytesToRead = _min(availableDataSize, FILE_DOWNLOAD_CHUNK_SIZE);
      Serial.println("Reading "+String(bytesToRead)+" bytes");
      stream->readBytes(fileBuffer, bytesToRead);
      file.write(fileBuffer, bytesToRead);
      downloadedDataSize += bytesToRead;
      Serial.println(String(downloadedDataSize)+" / "+String(FILE_SIZE));
      if (progressCallback) {
        progressCallback(downloadedDataSize, FILE_SIZE);
      }
    }
  }
  Serial.println("Downloaded file");
  free(fileBuffer);
}

String downloadFileToString(String url, String* errorMessage) {
  uint32_t connectionStatus = startWifi();
  if (connectionStatus == WIFI_CONNECTION_NOWIFI) {
    errorMessage->concat("Failed to start downloadFileToString from ");
    errorMessage->concat(url);
    errorMessage->concat(" because of missing WIFI connection");
    return "";
  }

  // Get file stream from internet
  HTTPClient httpClient;
  Serial.println("downloadFileToString()");
  httpClient.begin(url);
  int httpCode = httpClient.GET();
  if (httpCode != 200) {
    errorMessage->concat("HTTP error: "+String(httpCode));
    return "";
  }
  WiFiClient* stream = httpClient.getStreamPtr();

  // Download data and write into SD card
  size_t downloadedDataSize = 0;
  const size_t FILE_SIZE = httpClient.getSize();
  uint8_t* fileBuffer = (uint8_t*)heap_caps_malloc(FILE_DOWNLOAD_TO_STRING_MAX_SIZE+1, MALLOC_CAP_SPIRAM);
  String output = "";
  Serial.println("Starting download to string");
  while (downloadedDataSize < _min(FILE_SIZE, FILE_DOWNLOAD_TO_STRING_MAX_SIZE)) {
    size_t availableDataSize = stream->available();
    if (availableDataSize > 0) {
      uint32_t bytesToRead = _min(availableDataSize, FILE_DOWNLOAD_TO_STRING_MAX_SIZE);
      bytesToRead = _min(bytesToRead, FILE_DOWNLOAD_TO_STRING_MAX_SIZE-downloadedDataSize);
      Serial.println("Reading "+String(bytesToRead)+" bytes");
      stream->readBytes(fileBuffer, bytesToRead);
      fileBuffer[bytesToRead] = 0;
      output.concat((char*)fileBuffer);
      downloadedDataSize += bytesToRead;
      Serial.println(String(downloadedDataSize)+" / "+String(FILE_SIZE));
    }
  }
  Serial.println("Downloaded file to string");
  free(fileBuffer);
  return output;
}
