Dakkaron/PEPit/T-HMI-PEPmonitor/src/hardware/gfxHandler.hpp

#ifndef __GFXHANDLER_H__
#define __GFXHANDLER_H__
#include <Arduino.h>
#include <TFT_eSPI.h>
#include "matrix.h"

#define DISPLAY_T TFT_eSprite

extern TFT_eSPI tft;
extern TFT_eSprite spr;

#define FLIPPED_H 0x01
#define FLIPPED_V 0x02
#define DITHER_TRANSPARENCY 0x04

#define ALIGN_H_LEFT 0x00
#define ALIGN_H_CENTER 0x01
#define ALIGN_H_RIGHT 0x02
#define ALIGN_V_TOP 0x00
#define ALIGN_V_CENTER 0x04
#define ALIGN_V_BOTTOM 0x08

#define TRANSP_OFF 0x00
#define TRANSP_MASK 0x10

void initGfxHandler();
bool getBmpDimensions(String filename, int16_t* w, int16_t* h);
bool drawBmp(String filename, int16_t x, int16_t y, bool debugLog = true);
bool drawBmp(DISPLAY_T* sprite, String filename, int16_t x, int16_t y, bool debugLog = true);
bool loadBmp(DISPLAY_T* display, String filename);
bool loadBmp(DISPLAY_T* display, String filename, uint8_t options);
bool loadBmp(DISPLAY_T* display, String filename, uint8_t options, uint16_t maskingColor);
bool loadBmpAnim(DISPLAY_T** display, String filename, uint8_t animFrames);
bool loadBmpAnim(DISPLAY_T** display, String filename, uint8_t animFrames, uint8_t options);
bool loadBmpAnim(DISPLAY_T** displays, String filename, uint8_t animFrames, uint8_t options, uint16_t maskingColor);
void fillTriangle(DISPLAY_T* display, int32_t x0, int32_t y0, int32_t x1, int32_t y1, int32_t x2, int32_t y2, uint16_t color);
void fillQuad(DISPLAY_T* display, int32_t x0, int32_t y0, int32_t x1, int32_t y1, int32_t x2, int32_t y2, int32_t x3, int32_t y3, uint16_t color);
void drawSprite(DISPLAY_T* display, TFT_eSprite* sprite, int32_t dstX, int32_t dstY, int32_t maskingColor, float alpha, int32_t srcX=0, int32_t srcY=0, int32_t srcW=-1, int32_t srcH=-1, int32_t flags=0);
void drawSpriteScaled(DISPLAY_T* display, TFT_eSprite* sprite, Vector2D* position, Vector2D* scale, uint32_t flags, uint16_t maskColor, int16_t frameWidth, int16_t frameHeight, int16_t frameNr, float alpha);
void drawSpriteScaled(DISPLAY_T* display, TFT_eSprite* sprite, Vector2D* position, Vector2D* scale, uint32_t flags, uint16_t maskColor);
void drawSpriteTransformed(DISPLAY_T* display, TFT_eSprite* sprite, Vector2D* pos, Matrix2D* transform, uint32_t flags, uint16_t maskColor, int16_t frameWidth, int16_t frameHeight, int16_t frameNr, float alpha);
void drawSpriteTransformed(DISPLAY_T* display, TFT_eSprite* sprite, Vector2D* pos, Matrix2D* transform, uint32_t flags, uint16_t maskColor, int16_t frameWidth, int16_t frameHeight, int16_t frameNr);
void drawSpriteTransformed(DISPLAY_T* display, TFT_eSprite* sprite, Vector2D* pos, Matrix2D* transform, uint32_t flags, uint16_t maskColor, float alpha);
void drawProgressBar(DISPLAY_T* display, uint16_t progress, uint16_t greenOffset, int16_t x, int16_t y, int16_t w, int16_t h);
void drawProgressBar(DISPLAY_T* display, uint16_t val, uint16_t maxVal, uint16_t greenOffset, int16_t x, int16_t y, int16_t w, int16_t h);
void printShaded(DISPLAY_T* display, String text, uint8_t shadeStrength, uint16_t textColor, uint16_t shadeColor);
void printShaded(DISPLAY_T* display, String text, uint8_t shadeStrength, uint16_t textColor);
void printShaded(DISPLAY_T* display, String text, uint8_t shadeStrength);
void printShaded(DISPLAY_T* display, String text);
void drawSystemStats();
void drawImageButton(DISPLAY_T* display, String path, int16_t x, int16_t y, int16_t w, int16_t h, uint16_t color);
void drawButton(DISPLAY_T* display, String text, int16_t x, int16_t y, int16_t w, int16_t h, uint16_t color);
bool checkButton(int16_t x, int16_t y, int16_t w, int16_t h);
bool drawAndCheckImageButton(DISPLAY_T* display, String path, int16_t x, int16_t y, int16_t w, int16_t h, uint16_t color);
bool drawAndCheckButton(DISPLAY_T* display, String text, int16_t x, int16_t y, int16_t w, int16_t h, uint16_t color);
int16_t displayProfileSelection(DISPLAY_T* display, uint16_t nr, String* errorMessage);
int16_t displayGameSelection(DISPLAY_T* display, uint16_t nr, uint32_t requiredTaskTypes, String* errorMessage);
void drawKeyboard(DISPLAY_T* display, uint16_t keyColor, uint16_t textColor);
void checkKeyboard(DISPLAY_T* display, String* output, uint32_t maxCharacters, uint16_t keyColor, uint16_t textColor);
void checkFailWithMessage(String message);
void checkSoftFailWithMessage(String message, uint8_t textSize = 2);
void displayFullscreenMessage(String message, uint8_t textSize = 2);
void displayDateTimeSelection();

#endif /*__GFXHANDLER_H__*/
