Dakkaron/PEPit/PEPitCompat/compat/esp32-hal.h

/* PEPitCompat — ESP32 HAL Shim (stub, used by wifiHandler) */
#ifndef ESP32_HAL_H
#define ESP32_HAL_H

// Stub header — all HAL functions are no-op on Linux
// WiFi functionality is fully stubbed in WiFi.h

#endif // ESP32_HAL_H
