Dakkaron/PEPit/T-HMI-PEPmonitor/src/hardware/prefsHandler.h

#ifndef __PREFSHANDLER_H__
#define __PREFSHANDLER_H__
#include <Arduino.h>
#include <Preferences.h>

extern Preferences prefs;

void printNamespaces();
void dumpNamespaceContents();
bool backupAllPrefs();
bool restorePrefsBackup();
void setGamePrefsNamespace(String name);
void applyGamePrefsNamespace();
void clearPreferences();
void clearPreferencesExceptSystem();

#endif /* __PREFSHANDLER_H__ */
