Dakkaron/PEPit/T-HMI-PEPmonitor/src/hardware/touchHandler.h

#ifndef __TOUCH_HANDLER_H__
#define __TOUCH_HANDLER_H__

/******************************************************************************/
/***        include files                                                   ***/
/******************************************************************************/

#include <stdint.h>
#include "xpt2046.h"

/******************************************************************************/
/***        macro definitions                                               ***/
/******************************************************************************/

/******************************************************************************/
/***        type definitions                                                ***/
/******************************************************************************/

typedef struct touch_calibration_t
{
    uint16_t rawX;
    uint16_t rawY;
} touch_calibration_t;

/******************************************************************************/
/***        exported variables                                              ***/
/******************************************************************************/

extern XPT2046 touch;

/******************************************************************************/
/***        exported functions                                              ***/
/******************************************************************************/

void initTouch();
void runTouchCalibration();
bool isTouchInZone(int32_t x, int32_t y, int32_t w, int32_t h);

#endif /*__TOUCH_HANDLER_H__*/
