Dakkaron/PEPit/T-HMI-PEPmonitor/src/games/gameRacing.h

#ifndef __GAME_RACING_H__
#define __GAME_RACING_H__
#include <Arduino.h>

#include "constants.h"
#include "hardware/gfxHandler.hpp"
#include "hardware/sdHandler.h"
#include "hardware/touchHandler.h"
#include "hardware/prefsHandler.h"

#define DRAW_PLAYER_ALIVE     0b00000001
#define DRAW_PLAYER_DEAD      0b00000010
#define DRAW_PLAYER_DODGE     0b00000100
#define DRAW_ENEMY_ALIVE      0b00001000
#define DRAW_ENEMY_DEAD       0b00010000
#define DRAW_ENEMY_DODGE      0b00100000

void initGames_racing(String gamePath, GameConfig* gameConfig, String* errorMessage);
void drawShortBlowGame_racing(DISPLAY_T* display, BlowData* blowData, String* errorMessage);
void drawEqualBlowGame_racing(DISPLAY_T* display, BlowData* blowData, String* errorMessage);
void drawLongBlowGame_racing(DISPLAY_T* display, BlowData* blowData, String* errorMessage);
void drawTrampolineGame_racing(DISPLAY_T* display, JumpData* jumpData, String* errorMessage);
void drawInhalationGame_racing(DISPLAY_T* display, BlowData* blowData, String* errorMessage);
void drawInhalationBlowGame_racing(DISPLAY_T* display, BlowData* blowData, String* errorMessage);
bool displayProgressionMenu_racing(DISPLAY_T *display, String *errorMessage);

#define TRAINER_ANIM_PATH "gfx/trainer/brendan.bmp"

#endif /* __GAME_RACING_H__*/
